dominicbeesley/BlitterMk3-board/assets/6800.png

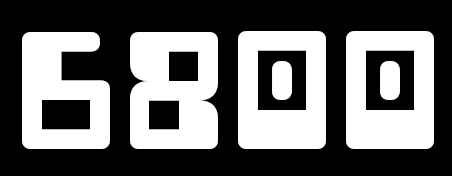
assets/6800.png
