dominicbeesley/BlitterMk3-board/testpinsquartus/mk3pinstest.vhd

-- Company: 			Dossytronics
-- Engineer: 			Dominic Beesley
-- 
-- Create Date:    	23/01/2021
-- Design Name: 
-- Module Name:    	dip 40 blitter - mk3 product board
-- Project Name: 
-- Target Devices: 
-- Tool versions: 
-- Description: 		PoC blitter and 6502/6809/Z80/68008 cpu board with 2M RAM, 256k ROM
-- Dependencies: 
--
-- Revision: 
-- Additional Comments: 
--
----------------------------------------------------------------------------------

library ieee;
use ieee.std_logic_1164.all;
use ieee.numeric_std.all;

library work;

entity mk3pinstest is
	generic (
		SIM									: boolean := false;							-- skip some stuff, i.e. slow sdram start up
		CLOCKSPEED							: natural := 128;								-- fast clock speed in mhz				
		G_DMA_CHANNELS						: natural := 2;
		G_SND_CHANNELS						: natural := 4;
		G_MASTER_COUNT						: natural := 9;
		G_SLAVE_COUNT						: natural := 10;
		G_JIM_DEVNO							: std_logic_vector(7 downto 0) := x"D1"
	);
	port(

		-- crystal osc 48Mhz - on WS board
		CLK_48M_i							: in		std_logic;

		-- 2M RAM/256K ROM bus (45)
		MEM_A_o								: out		std_logic_vector(20 downto 0);
		MEM_D_io								: inout	std_logic_vector(7 downto 0);	-- 17 bit RAMs used but D[7..0] is multiplexed with D[15..8]
		MEM_nOE_o							: out		std_logic;
		MEM_nWE_o							: out		std_logic;							-- add external pull-up

		MEM_FL_nCE_o						: out		std_logic;				
		MEM_RAM_nCE_o						: out		std_logic_vector(3 downto 0);
		
		-- 1 bit DAC sound out stereo, aux connectors mirror main (2)
		SND_L_o								: out		std_logic;
		SND_R_o								: out		std_logic;

		-- hdmi (11)

		HDMI_SCL_o							: out		std_logic;
		HDMI_SDA_io							: inout	std_logic;
		HDMI_HPD_i							: in		std_logic;
		HDMI_CK_o							: out		std_logic;
		HDMI_D0_o							: out		std_logic;
		HDMI_D1_o							: out		std_logic;
		HDMI_D2_o							: out		std_logic;
		
		-- sdcard (5)
		SD_CS_o								: out		std_logic;
		SD_CLK_o								: out		std_logic;
		SD_MOSI_o							: out		std_logic;
		SD_MISO_i							: in		std_logic;
		SD_DET_i								: in		std_logic;

		-- SYS bus connects to SYStem CPU socket (38)

		SUP_nRESET_i						: in		std_logic;								-- SYStem reset after supervisor

		SYS_A_o								: out		std_logic_vector(15 downto 0);
		SYS_D_io								: inout	std_logic_vector(7 downto 0);
		SYS_BUF_D_DIR_o					: out		std_logic;
		SYS_BUF_D_nOE_o					: out		std_logic;
		
		SYS_SYNC_o							: out		std_logic;
		SYS_PHI1_o							: out		std_logic;
		SYS_PHI2_o							: out		std_logic;
		SYS_RnW_o							: out		std_logic;

		SYS_RDY_i							: in		std_logic; -- Master only?
		SYS_nNMI_i							: in		std_logic;
		SYS_nIRQ_i							: in		std_logic;
		SYS_PHI0_i							: in		std_logic;
		SYS_nDBE_i							: in		std_logic;


		-- SYS configuration and auxiliary (18)
		SYS_AUX_io							: inout	std_logic_vector(6 downto 0);
		SYS_AUX_o							: out		std_logic_vector(3 downto 0);

		-- rpi interface (26)
		--rpi_gpio								: inout	std_logic_vector(27 downto 2);


		-- i2c EEPROM (2)
		I2C_SCL_o							: out		std_logic;
		I2C_SDA_io							: inout	std_logic;


		-- cpu / expansion sockets (56)

		exp_PORTA_io						: inout	std_logic_vector(7 downto 0);
		exp_PORTA_nOE_o					: out		std_logic;
		exp_PORTA_DIR_o					: out		std_logic;

		exp_PORTB_o							: out		std_logic_vector(7 downto 0);

		exp_PORTC_io						: inout 	std_logic_vector(11 downto 0);
		exp_PORTD_io						: inout	std_logic_vector(11 downto 0);

		exp_PORTEFG_io						: inout	std_logic_vector(11 downto 0);
		exp_PORTE_nOE						: out		std_logic;
		exp_PORTF_nOE						: out		std_logic;
		exp_PORTG_nOE						: out		std_logic;


		-- LEDs 
		LED_o									: out		std_logic_vector(3 downto 0);

		BTNUSER_i							: in		std_logic_vector(1 downto 0)



	);
end mk3pinstest;

architecture rtl of mk3pinstest is

begin

end rtl;
